liyuanhe211/ESP32_Env_Monitor/lib_SCD40.py

import machine
import time
from micropython import const


class SCD4X:
    """
    Based on https://github.com/adafruit/Adafruit_CircuitPython_SCD4X
    Copyright (c) 2021 ladyada for Adafruit Industries
    MIT License
    """

    DEFAULT_ADDRESS = 0x62
    DATA_READY = const(0xE4B8)
    STOP_PERIODIC_MEASUREMENT = const(0x3F86)
    START_PERIODIC_MEASUREMENT = const(0x21B1)
    READ_MEASUREMENT = const(0xEC05)

    def __init__(self, i2c_bus, address=DEFAULT_ADDRESS):
        self.i2c = i2c_bus
        self.address = address
        self._buffer = bytearray(18)
        self._cmd = bytearray(2)
        self._crc_buffer = bytearray(2)

        # cached readings
        self._temperature = -1
        self._relative_humidity = -1
        self._co2 = -1

        self.stop_periodic_measurement()

    def measure(self):
        """
        Measure once, return all three values.
        If failed, try again
        :return: (CO2, temp, humid)
        """

        # This for loop needs to exist otherwise the measurement will fail and a Nonetype can't be unpacked error will be given
        for _ in range(10):
            try:
                if self.data_ready:
                    self._read_data()
                break
            except OSError as e:
                print("Measuring failed:")
                print(e)
        return self._co2,self._temperature,self._relative_humidity

    @property
    def co2(self):
        """Returns the CO2 concentration in PPM (parts per million)
        .. note::
            Between measurements, the most recent reading will be cached and returned.
        """
        if self.data_ready:
            self._read_data()
        return self._co2

    @property
    def temperature(self):
        """Returns the current temperature in degrees Celsius
        .. note::
            Between measurements, the most recent reading will be cached and returned.
        """
        if self.data_ready:
            self._read_data()
        return self._temperature

    @property
    def relative_humidity(self):
        """Returns the current relative humidity in %rH.
        .. note::
            Between measurements, the most recent reading will be cached and returned.
        """
        if self.data_ready:
            self._read_data()
        return self._relative_humidity

    def _read_data(self):
        """Reads the temp/hum/co2 from the sensor and caches it"""
        self._send_command(self.READ_MEASUREMENT, cmd_delay=0.001)
        self._read_reply(self._buffer, 9)
        self._co2 = (self._buffer[0] << 8) | self._buffer[1]
        temp = (self._buffer[3] << 8) | self._buffer[4]
        self._temperature = -45 + 175 * (temp / 2 ** 16)
        humi = (self._buffer[6] << 8) | self._buffer[7]
        self._relative_humidity = 100 * (humi / 2 ** 16)

    @property
    def data_ready(self):
        """Check the sensor to see if new data is available"""
        self._send_command(self.DATA_READY, cmd_delay=0.001)
        self._read_reply(self._buffer, 3)
        return not ((self._buffer[0] & 0x03 == 0) and (self._buffer[1] == 0))

    def stop_periodic_measurement(self):
        """Stop measurement mode"""
        self._send_command(self.STOP_PERIODIC_MEASUREMENT, cmd_delay=0.5)

    def start_periodic_measurement(self):
        """Put sensor into working mode, about 5s per measurement"""
        self._send_command(self.START_PERIODIC_MEASUREMENT, cmd_delay=0.01)

    def _send_command(self, cmd, cmd_delay=0.0):
        self._cmd[0] = (cmd >> 8) & 0xFF
        self._cmd[1] = cmd & 0xFF
        self.i2c.writeto(self.address, self._cmd)
        time.sleep(cmd_delay)

    def _read_reply(self, buff, num):
        self.i2c.readfrom_into(self.address, buff, num)
        self._check_buffer_crc(self._buffer[0:num])

    def _check_buffer_crc(self, buf):
        for i in range(0, len(buf), 3):
            self._crc_buffer[0] = buf[i]
            self._crc_buffer[1] = buf[i + 1]
            if self._crc8(self._crc_buffer) != buf[i + 2]:
                raise RuntimeError("CRC check failed while reading data")
        return True

    @staticmethod
    def _crc8(buffer):
        crc = 0xFF
        for byte in buffer:
            crc ^= byte
            for _ in range(8):
                if crc & 0x80:
                    crc = (crc << 1) ^ 0x31
                else:
                    crc = crc << 1
        return crc & 0xFF  # return the bottom 8 bits
